Fred72z/ORIC/BUS_ORIC/Extensions/Communication_ACIA_RS232/README.md

# carte-ACIA_RS232

Cette platine se branche sur la platine d'extension de bus et permet d'ajouter une liaison série RS232 à l'ORIC (de 50 à 19200 bauds). 
Elle occupe les mêmes adresses que l'ACIA du telestrat soit 31C-31F

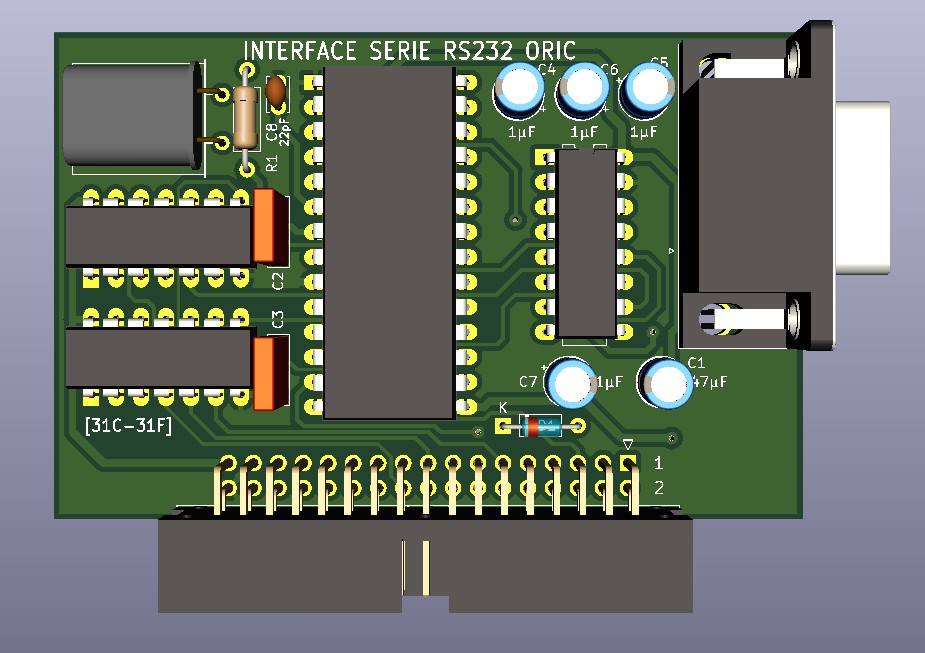
[picture p54: BUS_ORIC/Extensions/Communication_ACIA_RS232/Carte_ACIA_RS232.jpg]
Platine d'extension Optional Title
