Fred72z/ORIC/BUS_ORIC/Extensions/RTC/Implantation.png

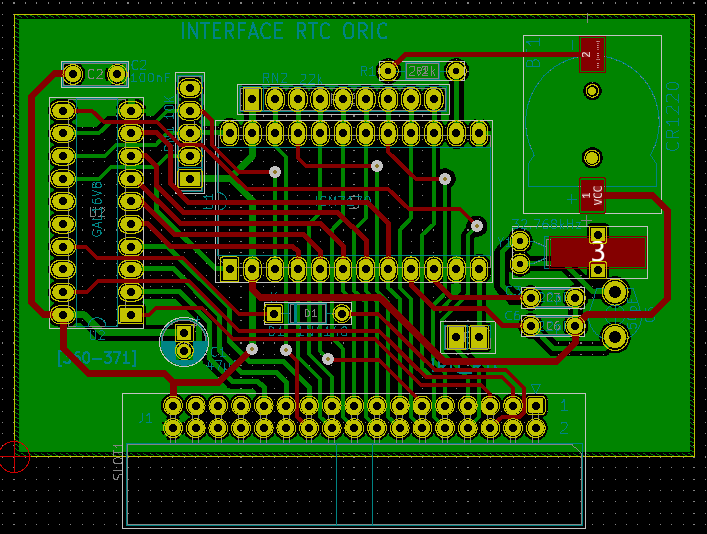
BUS_ORIC/Extensions/RTC/Implantation.png
