Fred72z/ORIC/EXP_Cartouche/Cartouches_titres.jpg

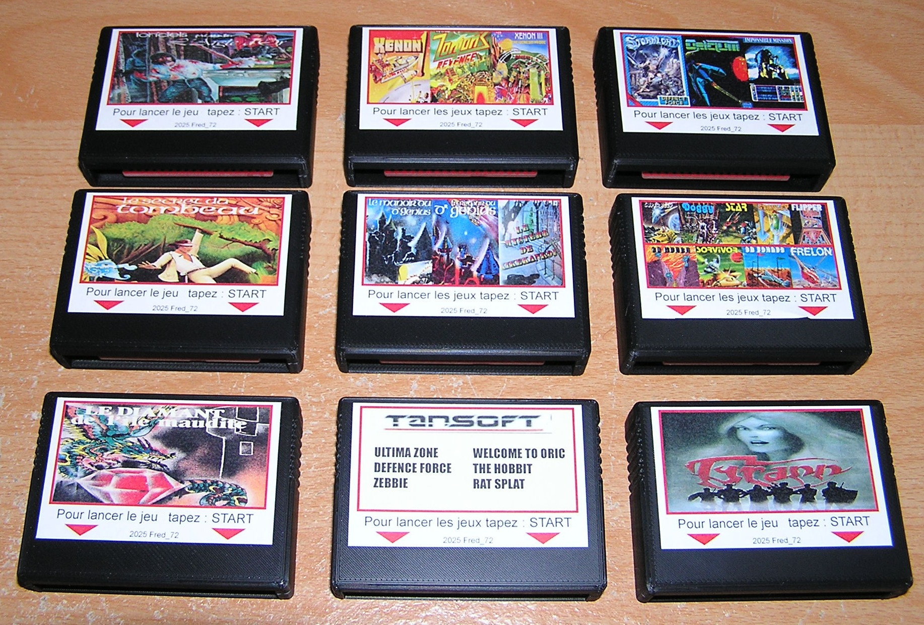
EXP_Cartouche/Cartouches_titres.jpg
