Fred72z/ORIC/EXP_Cartouche/Oric_EXP.jpg

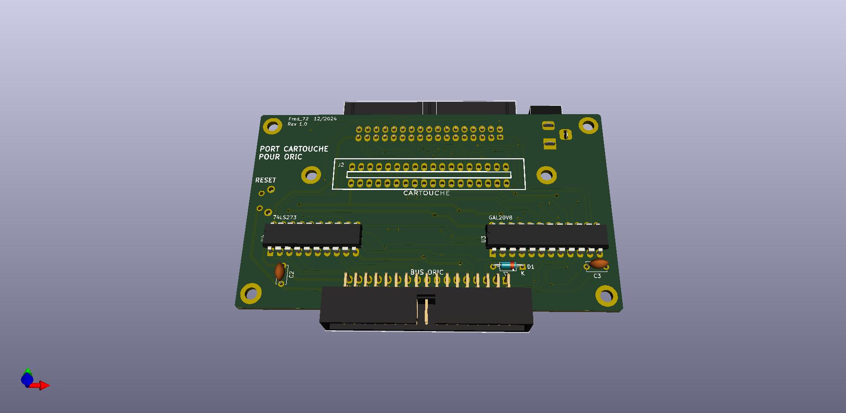
EXP_Cartouche/Oric_EXP.jpg
