Fred72z/ORIC/TELESTRAT III/TELESTRAT3.jpg

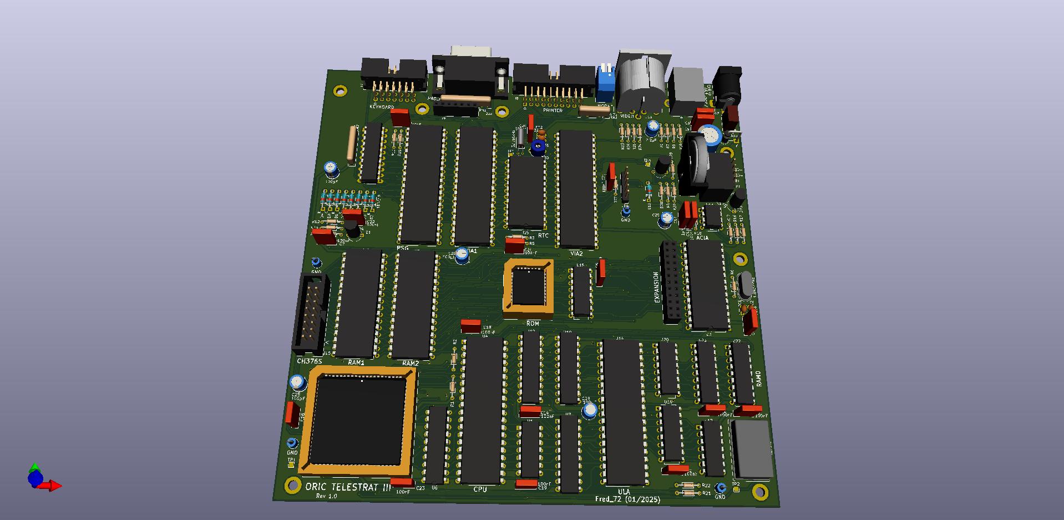
TELESTRAT III/TELESTRAT3.jpg
