Fred72z/ORIC/BUS_ORIC/Extensions/8ES_Numeriques/Interface 8ES Numériques.pdf

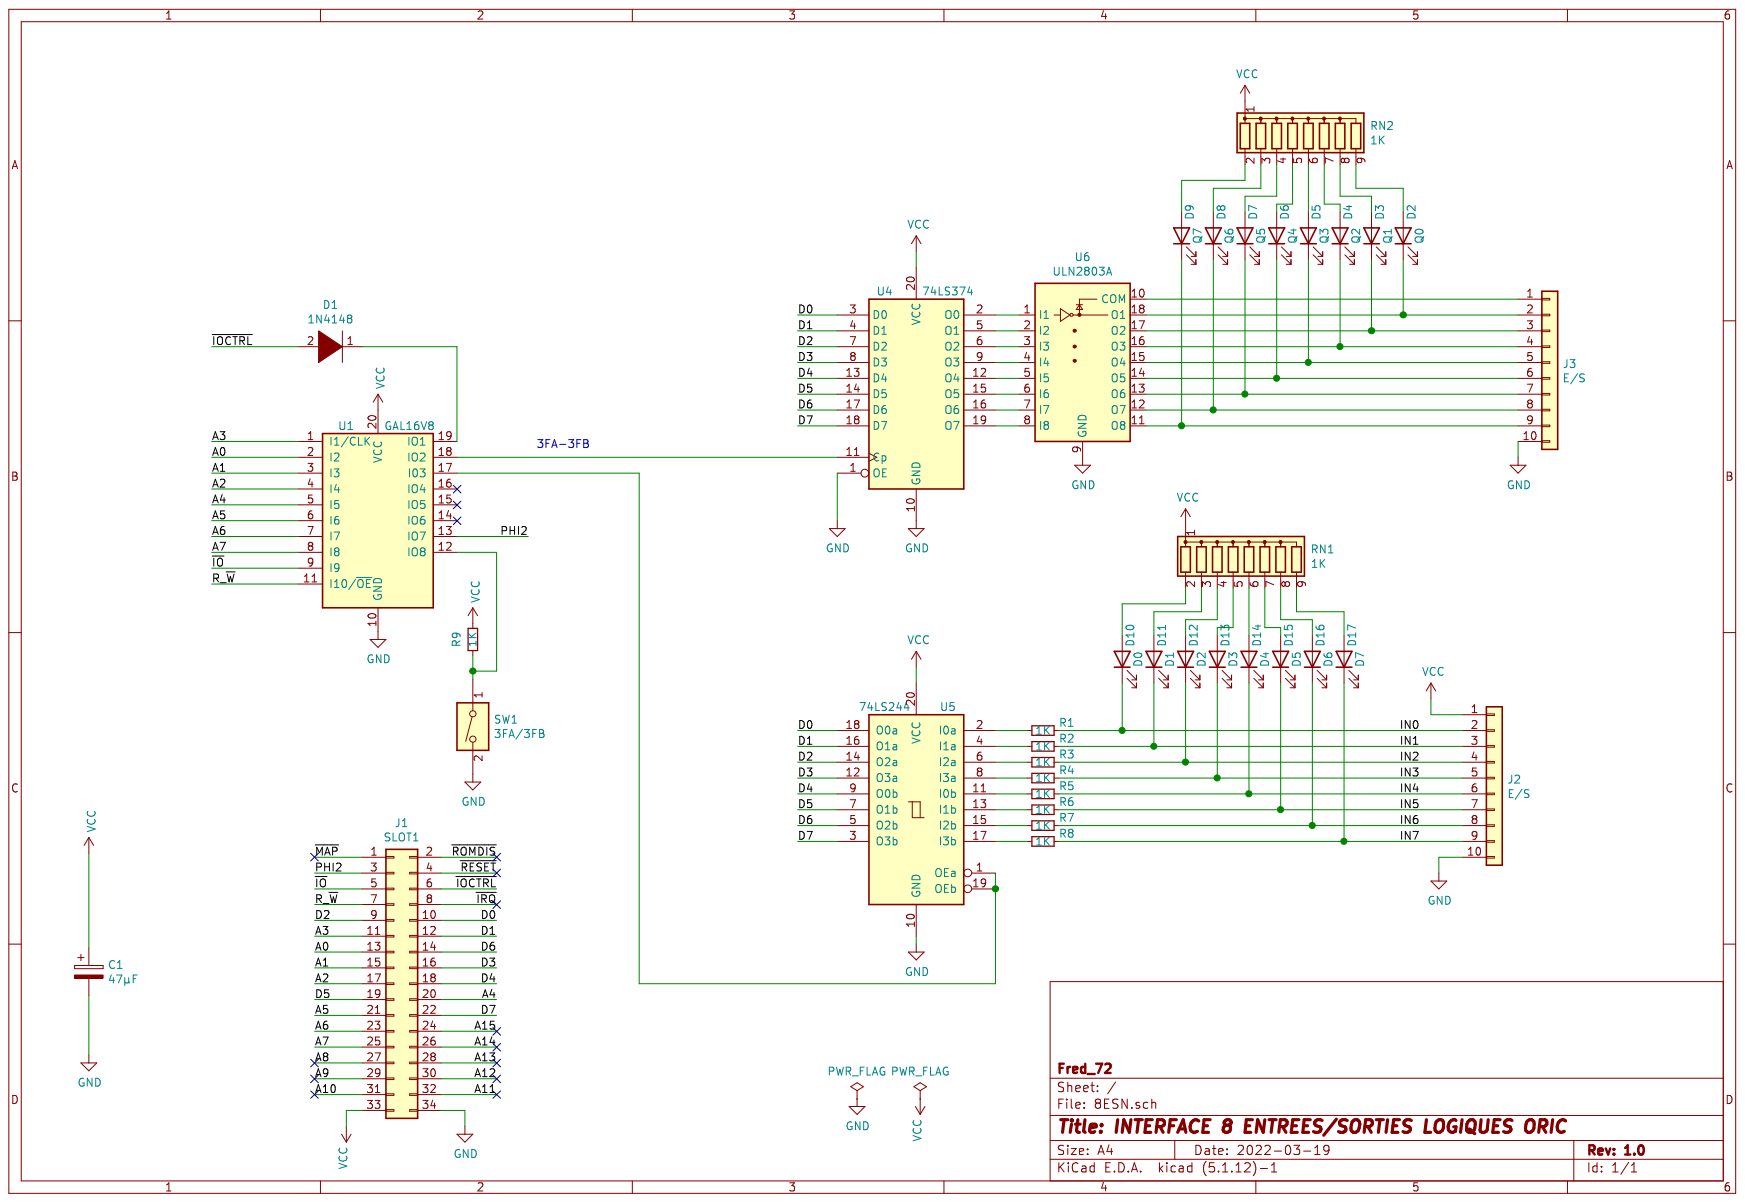
[picture p89: page 1]
