Fred72z/ORIC/BUS_ORIC/Extensions/Communication_ACIA_RS232/Schema ACIA.pdf

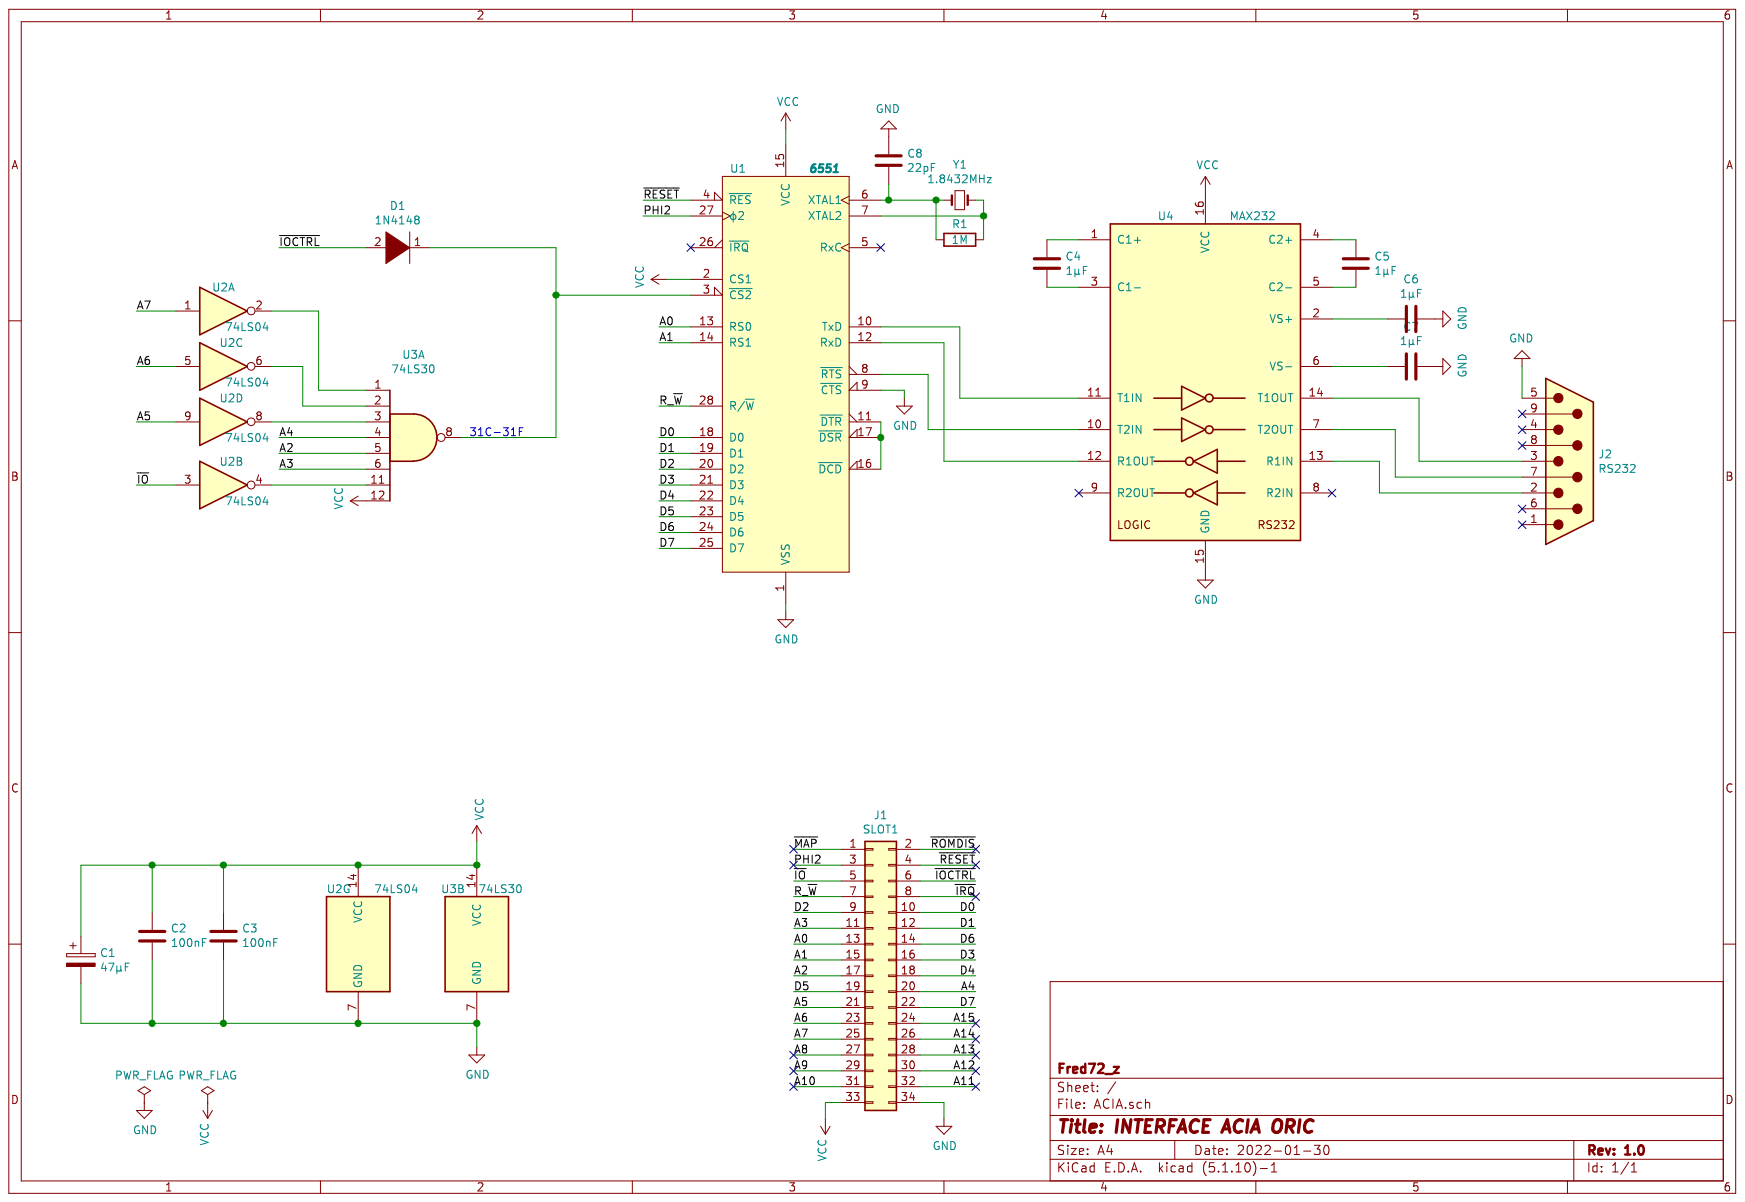
[picture p90: page 1]
