Fred72z/ORIC/Telestrat_II/Kicad5/Principale/Rev 2.2/Schéma Telestrat II rev 2.2.pdf

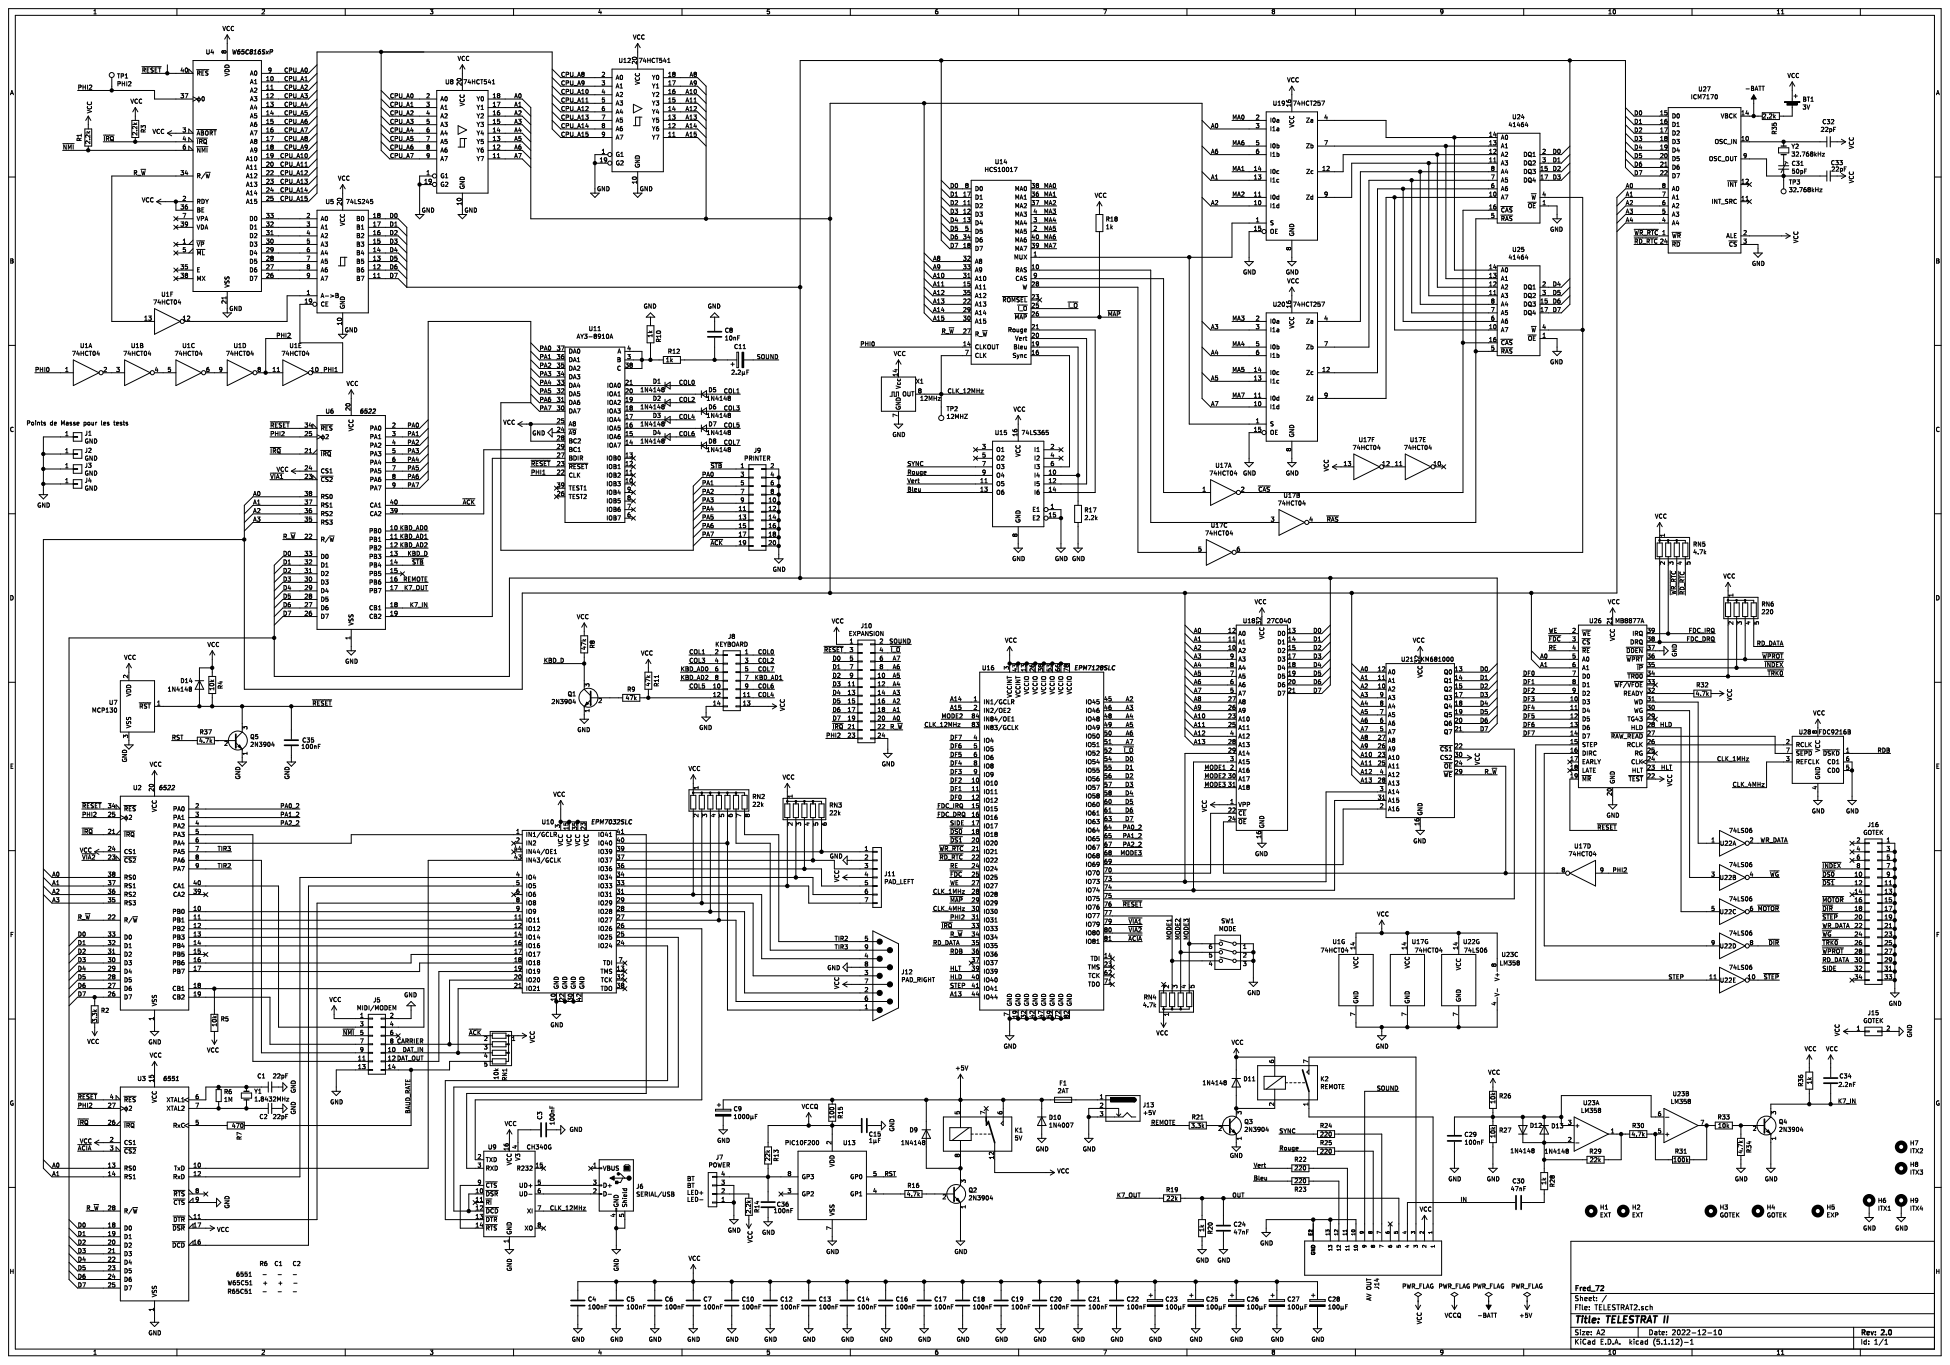
[picture p91: page 1]
