Fred72z/ORIC/Telestrat_II/Kicad5/Connectors/Rev 2.2/TELESTRAT II - Platine connecteurs.pdf

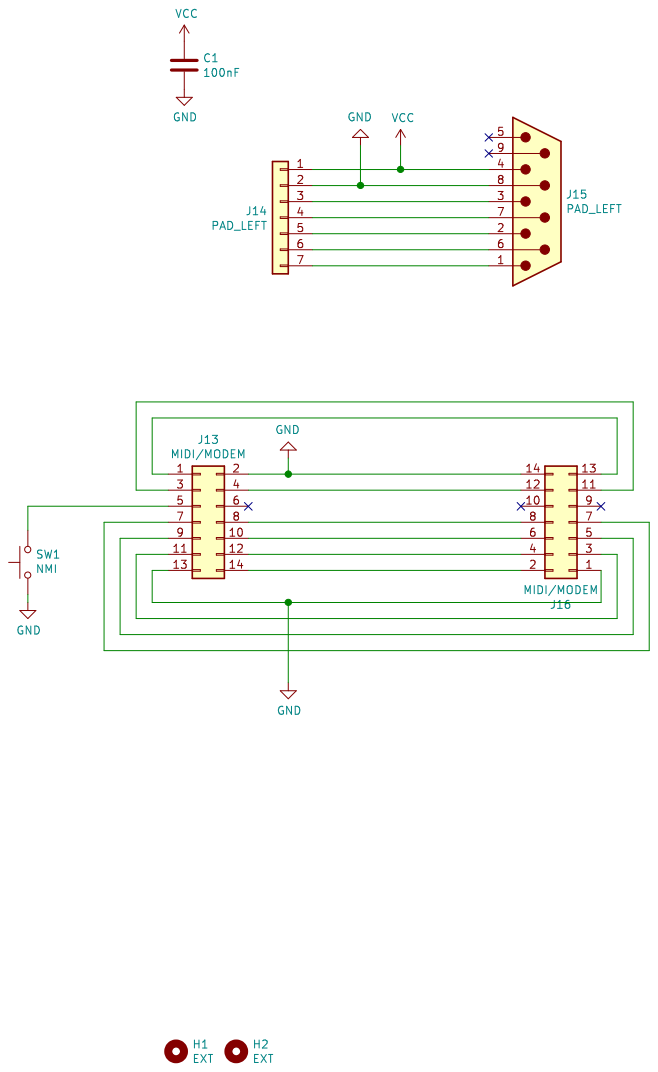
[picture p92: page 1]
