Fred72z/ORIC/Telestrat_II/Kicad5/Principale/Rev2.1/Schéma TELESTRAT II Rev 2.1.pdf

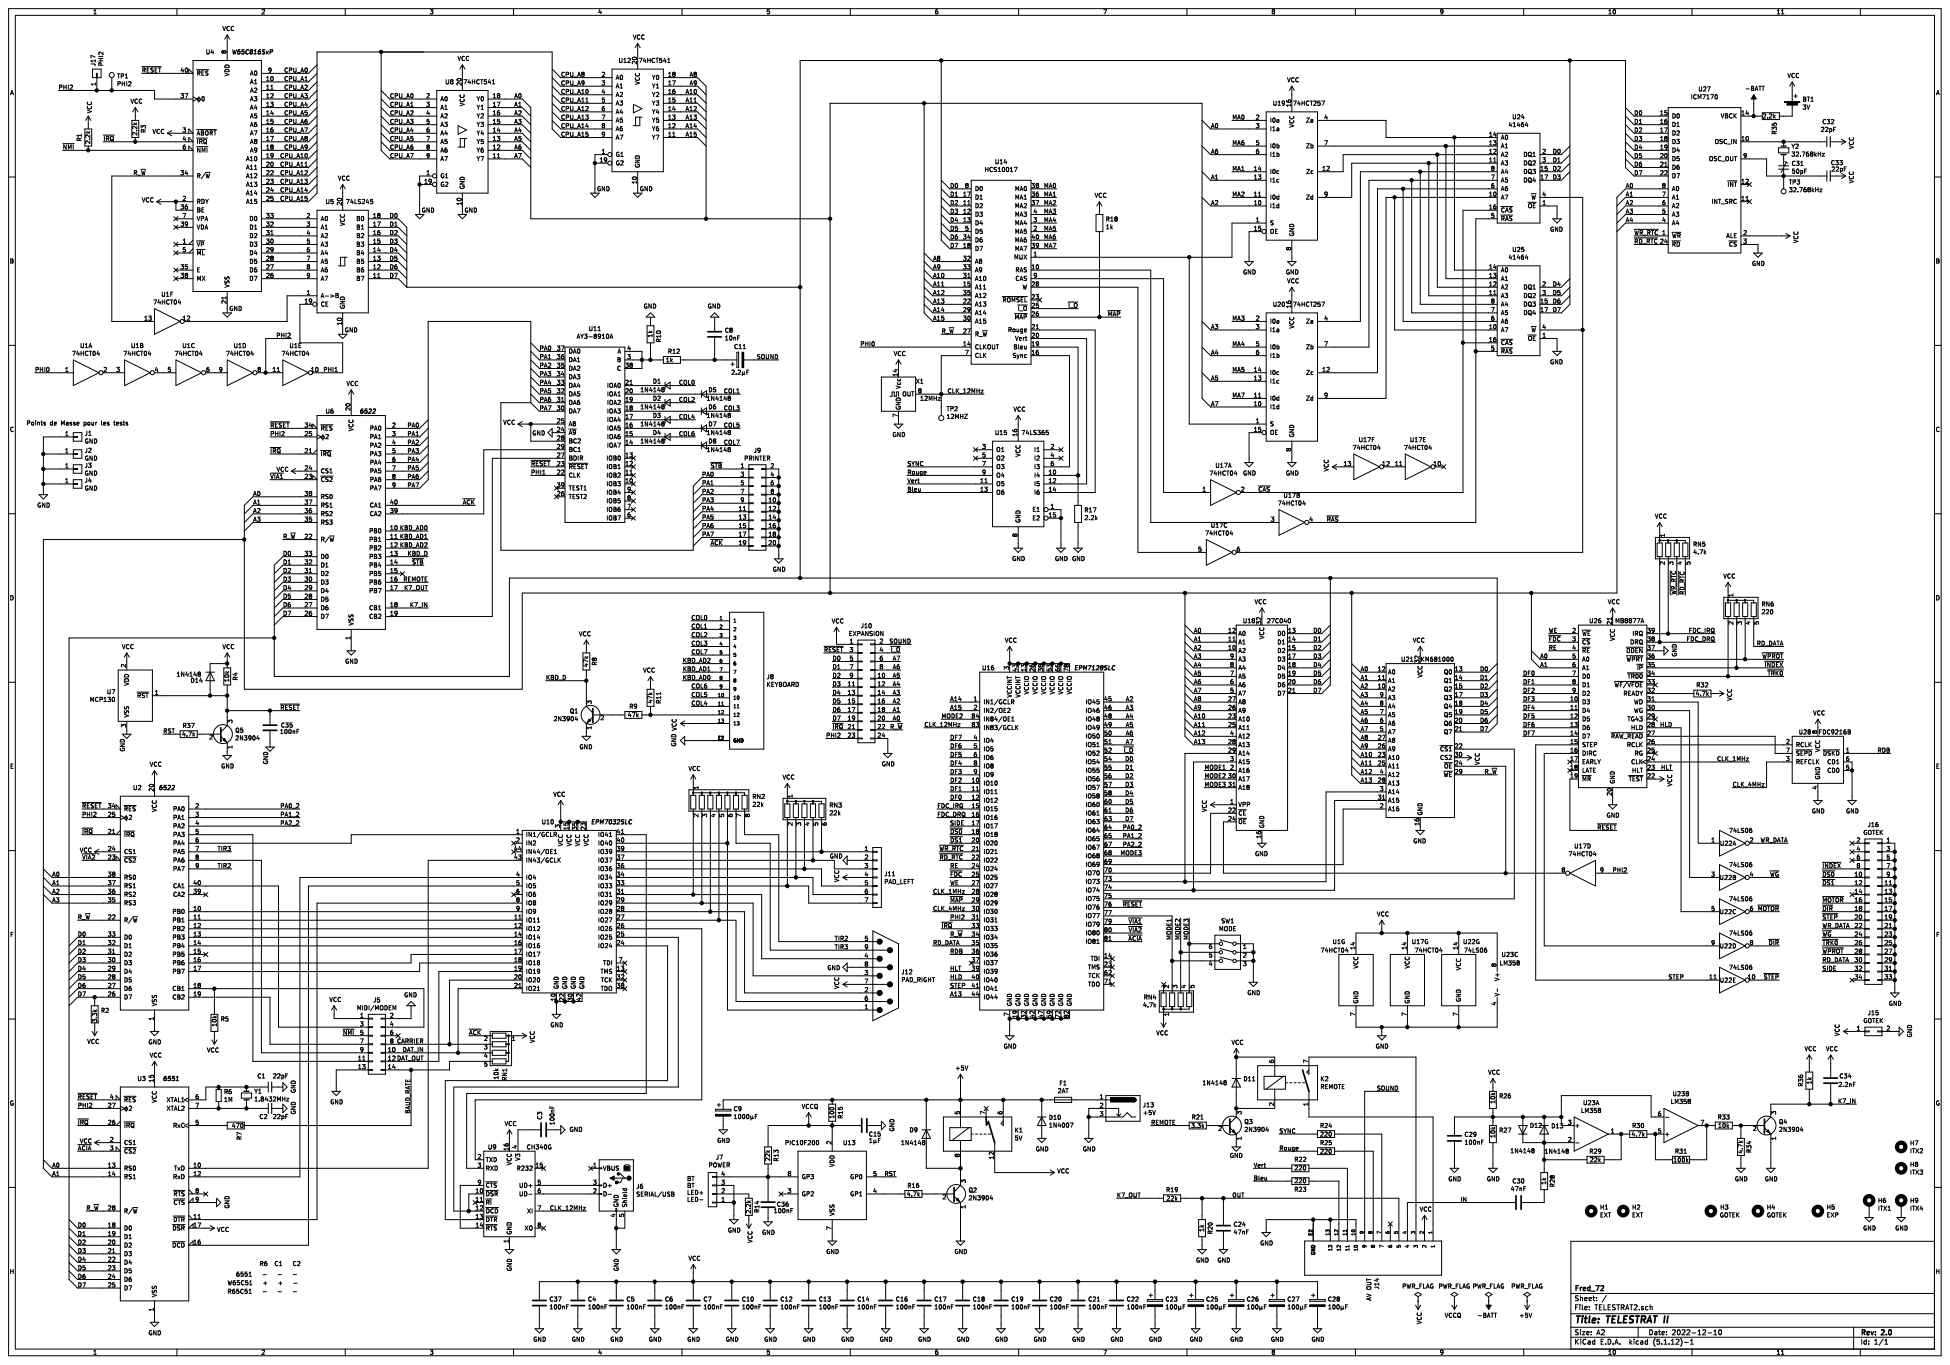
[picture p93: page 1]
