Fred72z/ORIC/BUS_ORIC/Extensions/8ES_Numeriques/Kicad5/8ESN.kicad_pcb

## KiCad design BUS_ORIC/Extensions/8ES_Numeriques/Kicad5/8ESN.kicad_pcb (2022-04-06)

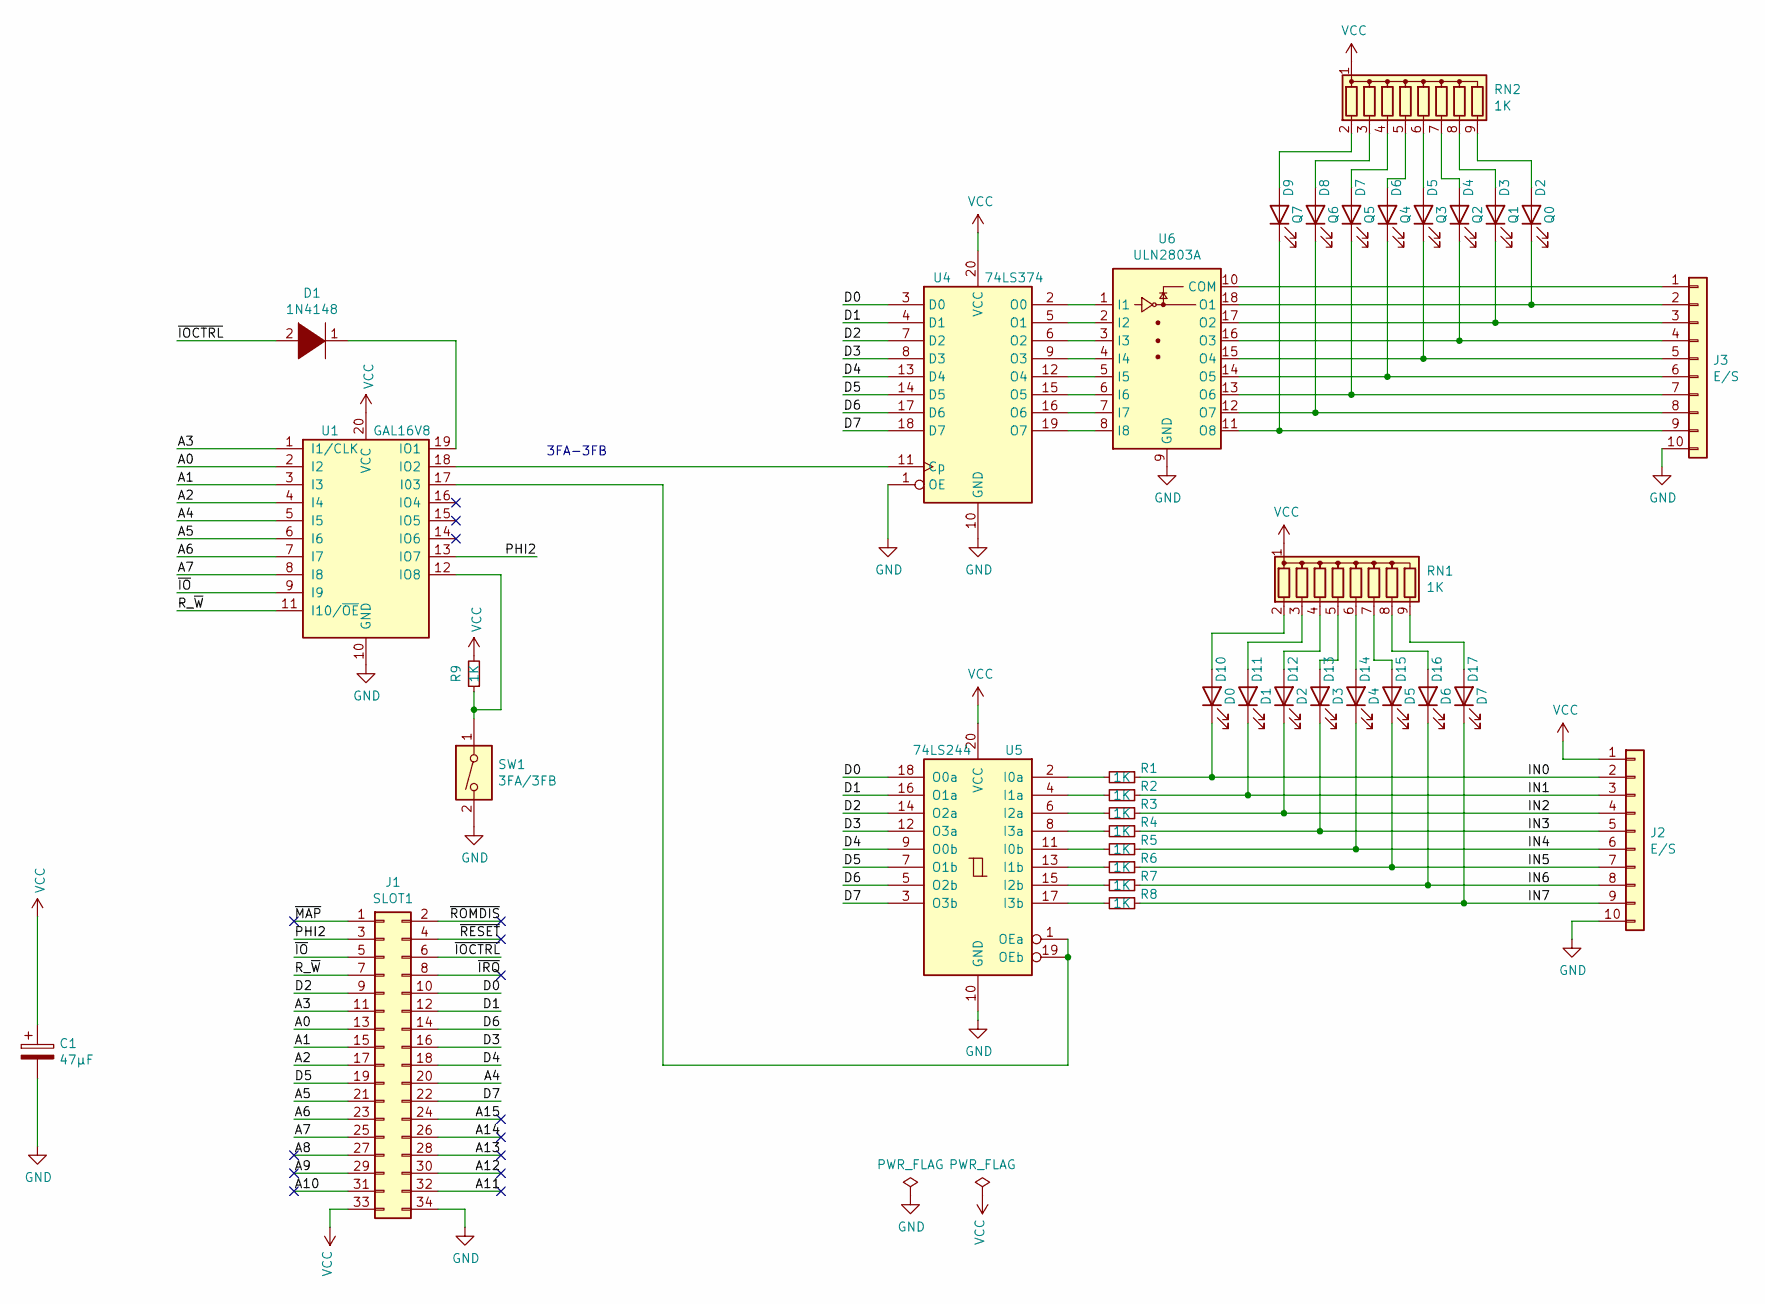
[picture p117: schematic 8ESN.sch, INTERFACE 8 ENTREES/SORTIES LOGIQUES ORIC]

Parts:
C1: 47µF; CP_Radial_D5.0mm_P2.00mm
D1: 1N4148; D_DO-35_SOD27_P7.62mm_Horizontal
D2: Q0; LED_0805_2012Metric
D3: Q1; LED_0805_2012Metric
D4: Q2; LED_0805_2012Metric
D5: Q3; LED_0805_2012Metric
D6: Q4; LED_0805_2012Metric
D7: Q5; LED_0805_2012Metric
D8: Q6; LED_0805_2012Metric
D9: Q7; LED_0805_2012Metric
D10: D0; LED_0805_2012Metric
D11: D1; LED_0805_2012Metric
D12: D2; LED_0805_2012Metric
D13: D3; LED_0805_2012Metric
D14: D4; LED_0805_2012Metric
D15: D5; LED_0805_2012Metric
D16: D6; LED_0805_2012Metric
D17: D7; LED_0805_2012Metric
J1: SLOT1; IDC-Header_2x17_P2.54mm_Horizontal
J2, J3: E/S; PinHeader_1x10_P2.54mm_Horizontal
R1, R2, R3, R4, R5, R6, R7, R8: 1K; R_Axial_DIN0204_L3.6mm_D1.6mm_P2.54mm_Vertical
R9: 1K; R_Axial_DIN0204_L3.6mm_D1.6mm_P7.62mm_Horizontal
RN1, RN2: 1K; R_Array_SIP9
SW1: 3FA/3FB; SW_DIP_SPSTx01_Slide_6.7x4.1mm_W7.62mm_P2.54mm_LowProfile
U1: GAL16V8; DIP-20_W7.62mm_LongPads
U4: 74LS374; DIP-20_W7.62mm_LongPads
U5: 74LS244; DIP-20_W7.62mm_LongPads
U6: ULN2803A; DIP-18_W7.62mm_LongPads

Connections:
/A0: J1.13, U1.2 (I2)
/A1: J1.15, U1.3 (I3)
/A2: J1.17, U1.4 (I4)
/A3: J1.11, U1.1 (I1/CLK)
/A4: J1.20, U1.5 (I5)
/A5: J1.21, U1.6 (I6)
/A6: J1.23, U1.7 (I7)
/A7: J1.25, U1.8 (I8)
/A8: J1.27
/A9: J1.29
/A10: J1.31
/A11: J1.32
/A12: J1.30
/A13: J1.28
/A14: J1.26
/A15: J1.24
/D0: J1.10, U4.3 (D0), U5.18 (O0a)
/D1: J1.12, U4.4 (D1), U5.16 (O1a)
/D2: J1.9, U4.7 (D2), U5.14 (O2a)
/D3: J1.16, U4.8 (D3), U5.12 (O3a)
/D4: J1.18, U4.13 (D4), U5.9 (O0b)
/D5: J1.19, U4.14 (D5), U5.7 (O1b)
/D6: J1.14, U4.17 (D6), U5.5 (O2b)
/D7: J1.22, U4.18 (D7), U5.3 (O3b)
/IN0: D10.1 (K), J2.2, R1.1
/IN1: D11.1 (K), J2.3, R2.1
/IN2: D12.1 (K), J2.4, R3.1
/IN3: D13.1 (K), J2.5, R4.1
/IN4: D14.1 (K), J2.6, R5.1
/IN5: D15.1 (K), J2.7, R6.1
/IN6: D16.1 (K), J2.8, R7.1
/IN7: D17.1 (K), J2.9, R8.1
/PHI2: J1.3, U1.13 (IO7)
/R_~W: J1.7, U1.11 (I10/~OE~)
/~IO: J1.5, U1.9 (I9)
/~IOCTRL: D1.2 (A), J1.6
/~IRQ: J1.8
/~MAP: J1.1
/~RESET: J1.4
/~ROMDIS: J1.2
GND: C1.2, J1.34, J2.10, J3.10, SW1.2, U1.10 (GND), U4.1 (OE), U4.10 (GND), U5.10 (GND), U6.9 (GND)
unnamed: D1.1 (K), U1.19 (IO1)
unnamed: D2.1 (K), J3.2, U6.18 (O1)
unnamed: D2.2 (A), RN2.9 (R8)
unnamed: D3.1 (K), J3.3, U6.17 (O2)
unnamed: D3.2 (A), RN2.8 (R7)
unnamed: D4.1 (K), J3.4, U6.16 (O3)
unnamed: D4.2 (A), RN2.7 (R6)
unnamed: D5.1 (K), J3.5, U6.15 (O4)
unnamed: D5.2 (A), RN2.6 (R5)
unnamed: D6.1 (K), J3.6, U6.14 (O5)
unnamed: D6.2 (A), RN2.5 (R4)
unnamed: D7.1 (K), J3.7, U6.13 (O6)
unnamed: D7.2 (A), RN2.4 (R3)
unnamed: D8.1 (K), J3.8, U6.12 (O7)
unnamed: D8.2 (A), RN2.3 (R2)
unnamed: D9.1 (K), J3.9, U6.11 (O8)
unnamed: D9.2 (A), RN2.2 (R1)
unnamed: D10.2 (A), RN1.2 (R1)
unnamed: D11.2 (A), RN1.3 (R2)
unnamed: D12.2 (A), RN1.4 (R3)
unnamed: D13.2 (A), RN1.5 (R4)
unnamed: D14.2 (A), RN1.6 (R5)
unnamed: D15.2 (A), RN1.7 (R6)
unnamed: D16.2 (A), RN1.8 (R7)
unnamed: D17.2 (A), RN1.9 (R8)
unnamed: J3.1, U6.10 (COM)
unnamed: R1.2, U5.2 (I0a)
unnamed: R2.2, U5.4 (I1a)
unnamed: R3.2, U5.6 (I2a)
unnamed: R4.2, U5.8 (I3a)
unnamed: R5.2, U5.11 (I0b)
unnamed: R6.2, U5.13 (I1b)
unnamed: R7.2, U5.15 (I2b)
unnamed: R8.2, U5.17 (I3b)
unnamed: R9.1, SW1.1, U1.12 (IO8)
unnamed: U1.17 (I03), U5.1 (OEa), U5.19 (OEb)
unnamed: U1.18 (IO2), U4.11 (Cp)
unnamed: U4.2 (O0), U6.1 (I1)
unnamed: U4.5 (O1), U6.2 (I2)
unnamed: U4.6 (O2), U6.3 (I3)
unnamed: U4.9 (O3), U6.4 (I4)
unnamed: U4.12 (O4), U6.5 (I5)
unnamed: U4.15 (O5), U6.6 (I6)
unnamed: U4.16 (O6), U6.7 (I7)
unnamed: U4.19 (O7), U6.8 (I8)
VCC: C1.1, J1.33, J2.1, R9.2, RN1.1 (common), RN2.1 (common), U1.20 (VCC), U4.20 (VCC), U5.20 (VCC)

Notes on the sheet:
3FA-3FB

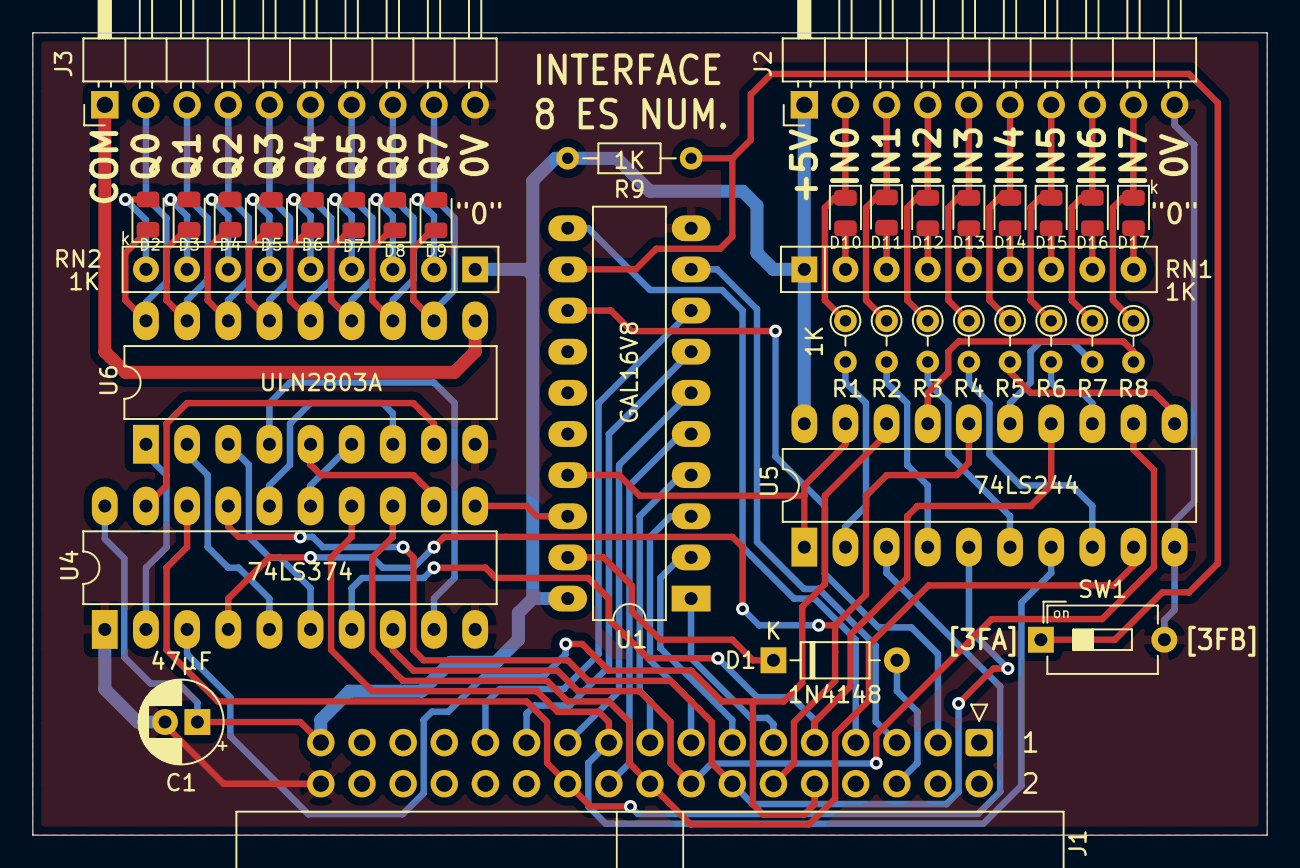
[picture p118: board 8ESN.kicad_pcb from above]

Board: 2 copper layers, 76.2 x 49.5 mm, 37 parts (0 on the bottom side), 75 nets.
