Fred72z/ORIC/BUS_ORIC/Kicad5/Oric_BUS.kicad_pcb

## KiCad design BUS_ORIC/Kicad5/Oric_BUS.kicad_pcb (2022-04-06)

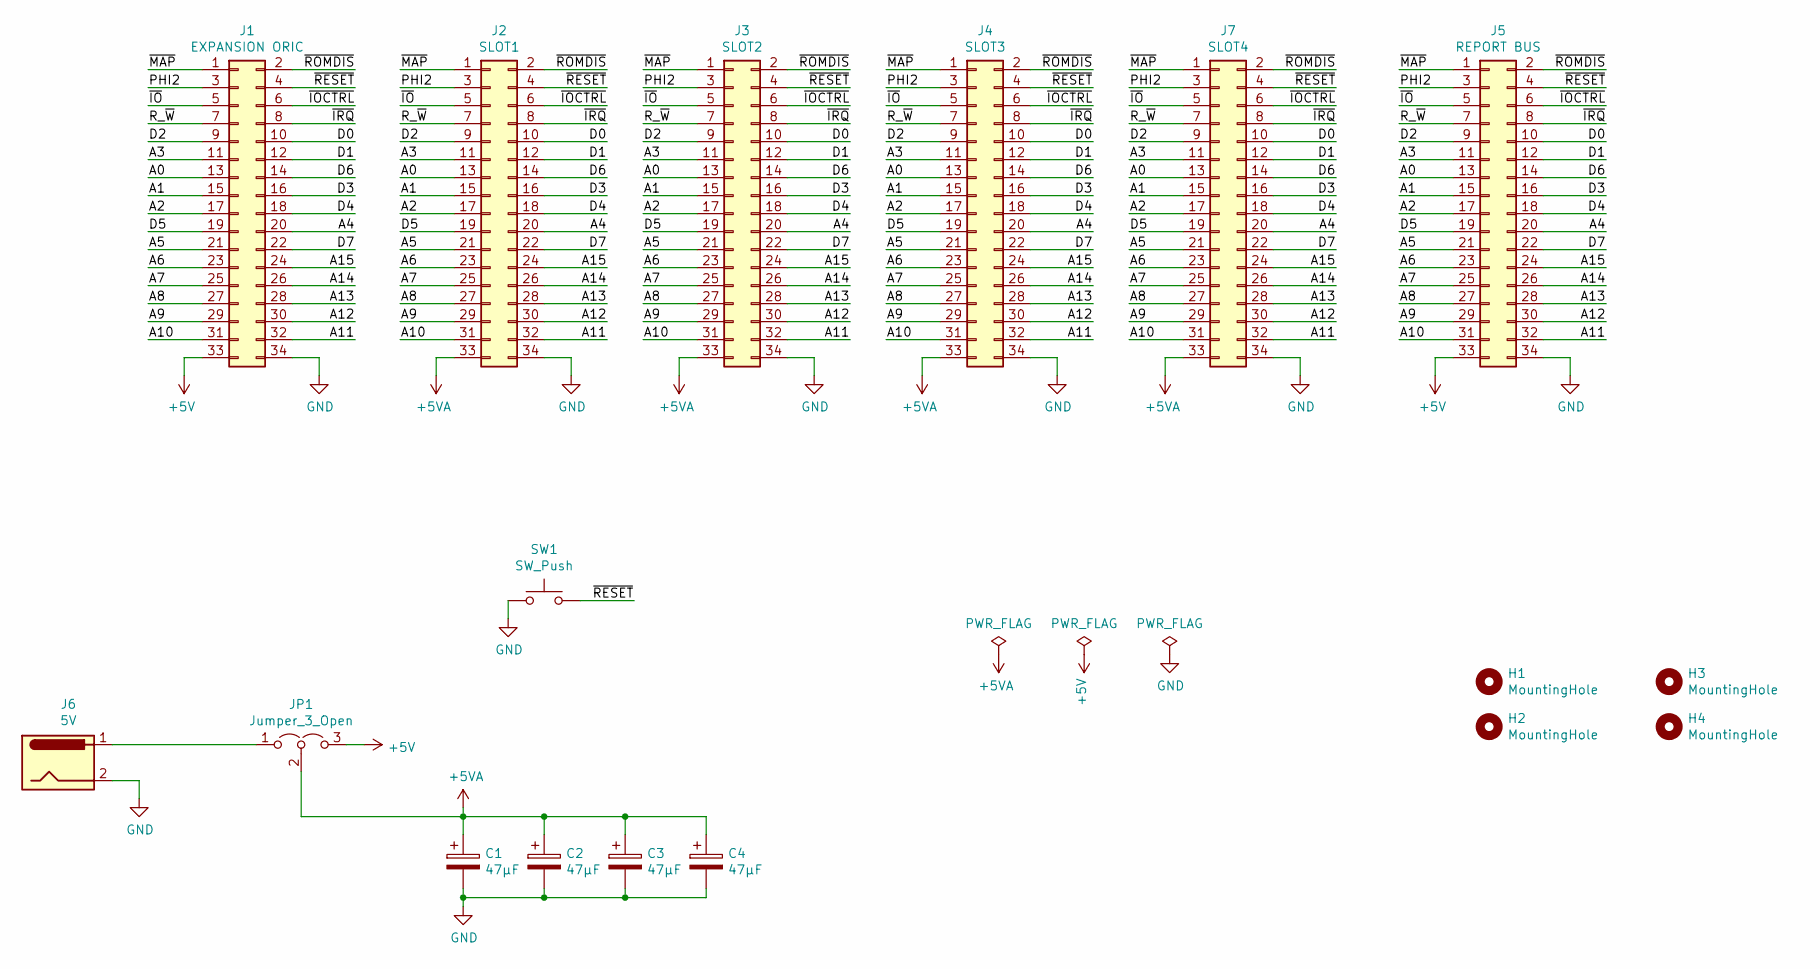
[picture p119: schematic Oric_BUS.sch, PLATINE BUS ORIC]

Parts:
C1, C2, C3, C4: 47µF; CP_Radial_D5.0mm_P2.00mm_Horizontal
H1, H2, H3, H4: MountingHole; MountingHole_3.2mm_M3
J1: EXPANSION ORIC; IDC-Header_2x17_P2.54mm_Vertical
J2: SLOT1; PinSocket_2x17_P2.54mm_Vertical
J3: SLOT2; PinSocket_2x17_P2.54mm_Vertical
J4: SLOT3; PinSocket_2x17_P2.54mm_Vertical
J5: REPORT BUS; IDC-Header_2x17_P2.54mm_Vertical
J6: 5V; BarrelJack_Horizontal
J7: SLOT4; PinSocket_2x17_P2.54mm_Vertical
JP1: Jumper_3_Open; PinHeader_1x03_P2.54mm_Vertical
SW1: SW_Push; SW_Tactile_SPST_Angled_PTS645Vx39-2LFS

Connections:
+5V: J1.33, J5.33, JP1.3 (B)
+5VA: C1.1, C2.1, C3.1, C4.1, J2.33, J3.33, J4.33, J7.33, JP1.2 (C)
/A0: J1.13, J2.13, J3.13, J4.13, J5.13, J7.13
/A1: J1.15, J2.15, J3.15, J4.15, J5.15, J7.15
/A2: J1.17, J2.17, J3.17, J4.17, J5.17, J7.17
/A3: J1.11, J2.11, J3.11, J4.11, J5.11, J7.11
/A4: J1.20, J2.20, J3.20, J4.20, J5.20, J7.20
/A5: J1.21, J2.21, J3.21, J4.21, J5.21, J7.21
/A6: J1.23, J2.23, J3.23, J4.23, J5.23, J7.23
/A7: J1.25, J2.25, J3.25, J4.25, J5.25, J7.25
/A8: J1.27, J2.27, J3.27, J4.27, J5.27, J7.27
/A9: J1.29, J2.29, J3.29, J4.29, J5.29, J7.29
/A10: J1.31, J2.31, J3.31, J4.31, J5.31, J7.31
/A11: J1.32, J2.32, J3.32, J4.32, J5.32, J7.32
/A12: J1.30, J2.30, J3.30, J4.30, J5.30, J7.30
/A13: J1.28, J2.28, J3.28, J4.28, J5.28, J7.28
/A14: J1.26, J2.26, J3.26, J4.26, J5.26, J7.26
/A15: J1.24, J2.24, J3.24, J4.24, J5.24, J7.24
/D0: J1.10, J2.10, J3.10, J4.10, J5.10, J7.10
/D1: J1.12, J2.12, J3.12, J4.12, J5.12, J7.12
/D2: J1.9, J2.9, J3.9, J4.9, J5.9, J7.9
/D3: J1.16, J2.16, J3.16, J4.16, J5.16, J7.16
/D4: J1.18, J2.18, J3.18, J4.18, J5.18, J7.18
/D5: J1.19, J2.19, J3.19, J4.19, J5.19, J7.19
/D6: J1.14, J2.14, J3.14, J4.14, J5.14, J7.14
/D7: J1.22, J2.22, J3.22, J4.22, J5.22, J7.22
/PHI2: J1.3, J2.3, J3.3, J4.3, J5.3, J7.3
/R_~W: J1.7, J2.7, J3.7, J4.7, J5.7, J7.7
/~IO: J1.5, J2.5, J3.5, J4.5, J5.5, J7.5
/~IOCTRL: J1.6, J2.6, J3.6, J4.6, J5.6, J7.6
/~IRQ: J1.8, J2.8, J3.8, J4.8, J5.8, J7.8
/~MAP: J1.1, J2.1, J3.1, J4.1, J5.1, J7.1
/~RESET: J1.4, J2.4, J3.4, J4.4, J5.4, J7.4, SW1.2
/~ROMDIS: J1.2, J2.2, J3.2, J4.2, J5.2, J7.2
GND: C1.2, C2.2, C3.2, C4.2, J1.34, J2.34, J3.34, J4.34, J5.34, J6.2, J7.34, SW1.1
unnamed: J6.1, JP1.1 (A)

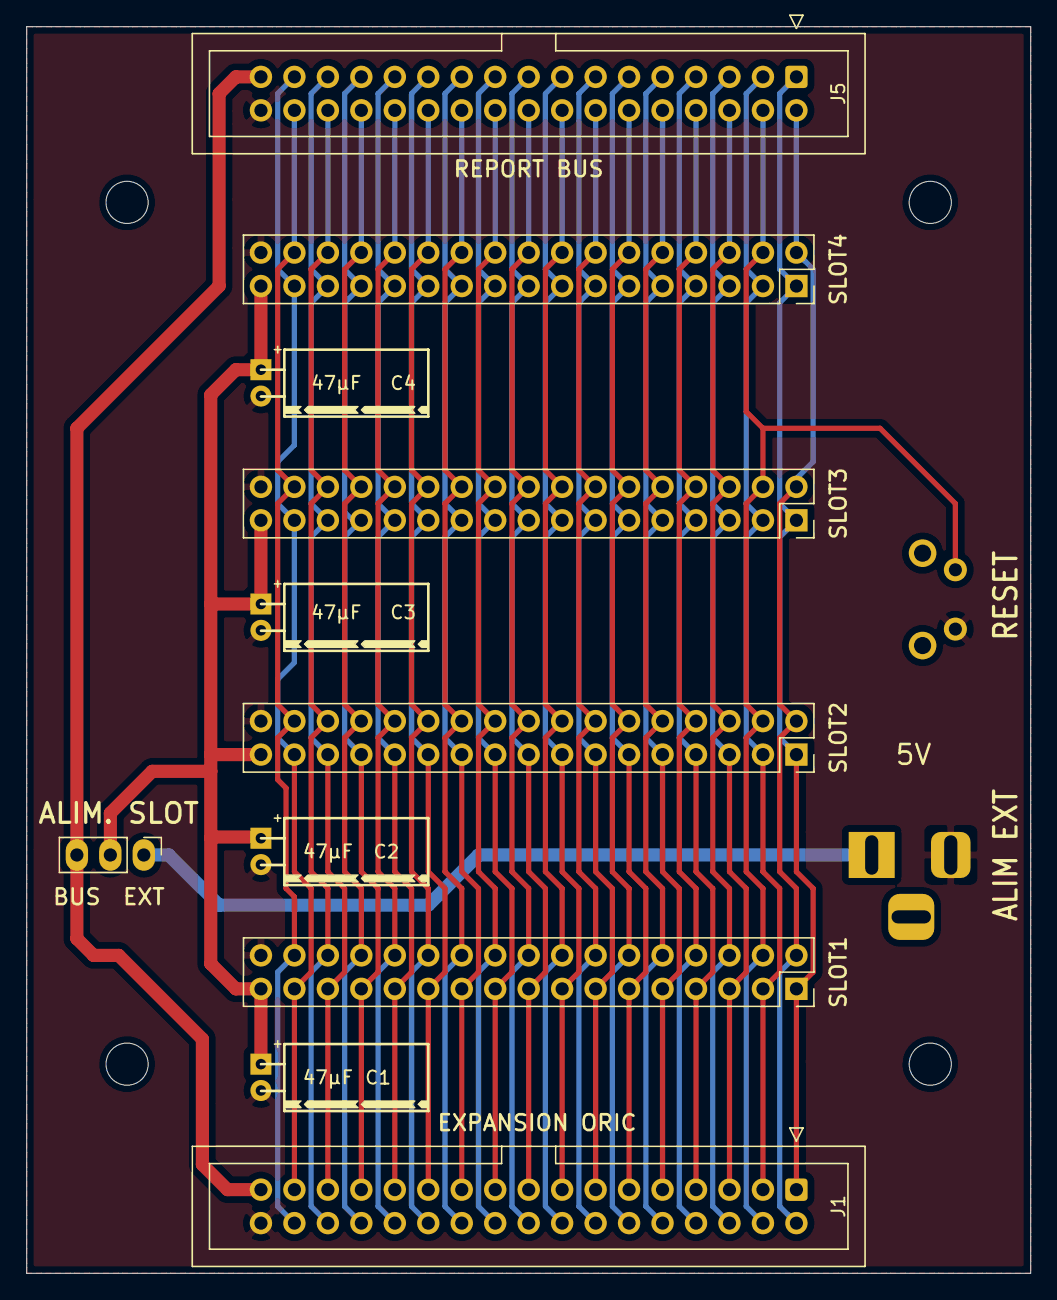
[picture p120: board Oric_BUS.kicad_pcb from above]

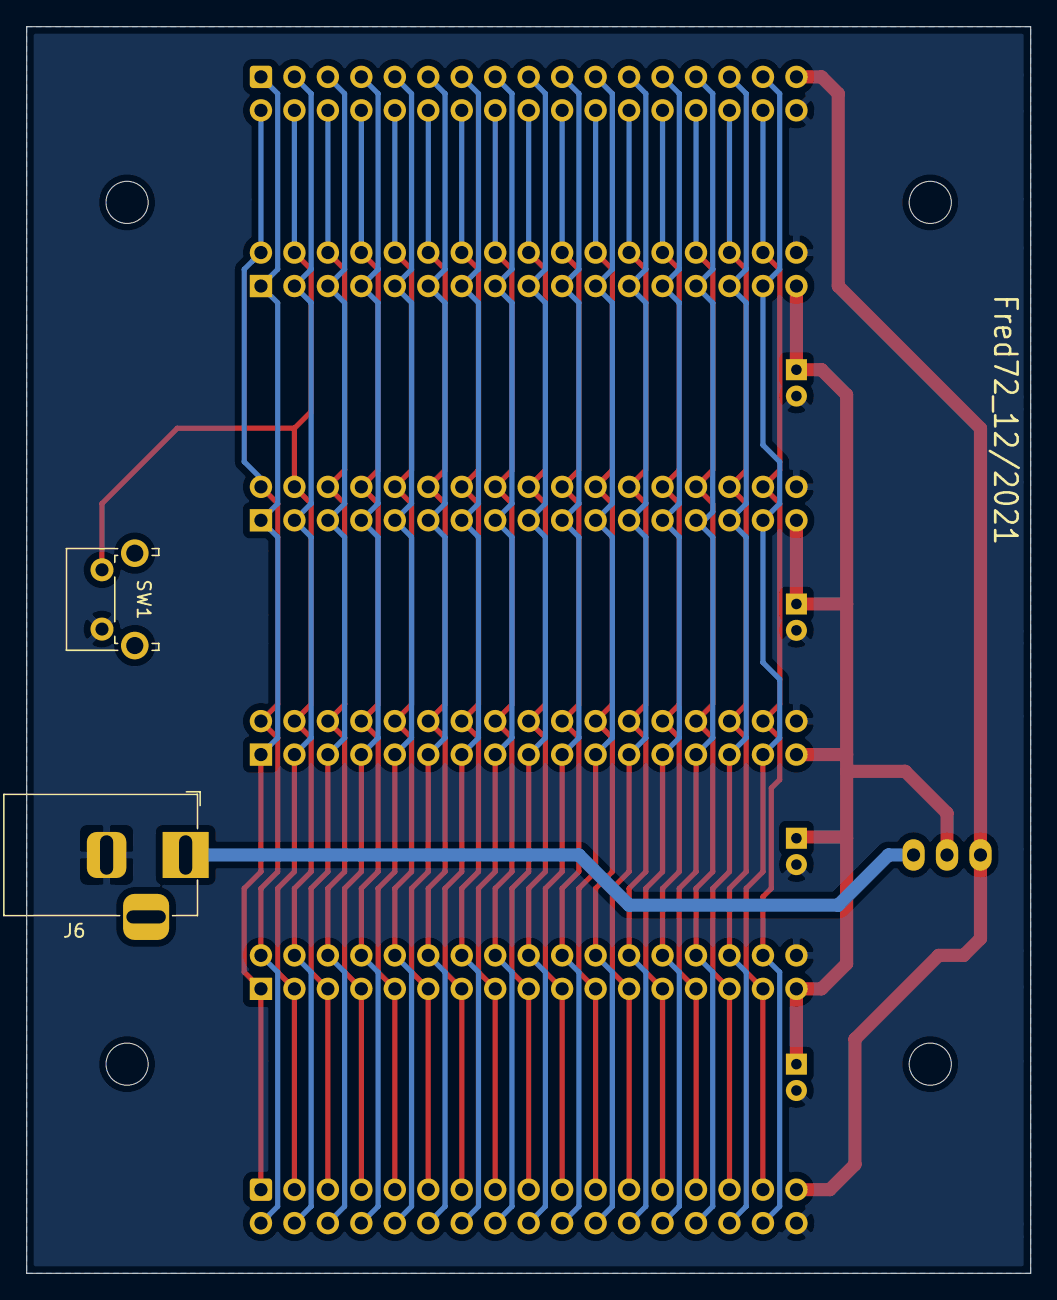
[picture p121: board Oric_BUS.kicad_pcb from below]

Board: 2 copper layers, 76.2 x 94.6 mm, 17 parts (2 on the bottom side), 36 nets.
